aaronbot3000/velociryder/solidworks model/sprocket-encoder-12-new.sldprt

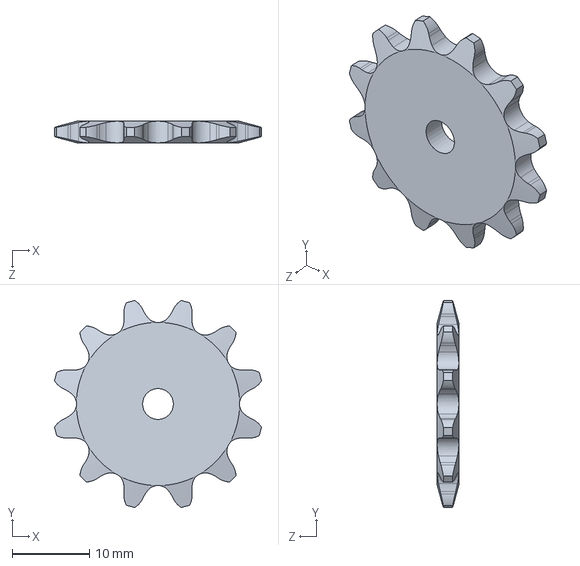
[picture p15: CAD file, 2012-03-13]
solidworks model/sprocket-encoder-12-new.sldprt
26.8 x 26.8 x 2.79 mm
