aaronbot3000/velociryder/solidworks model/sprocket-wheel-43.sldprt

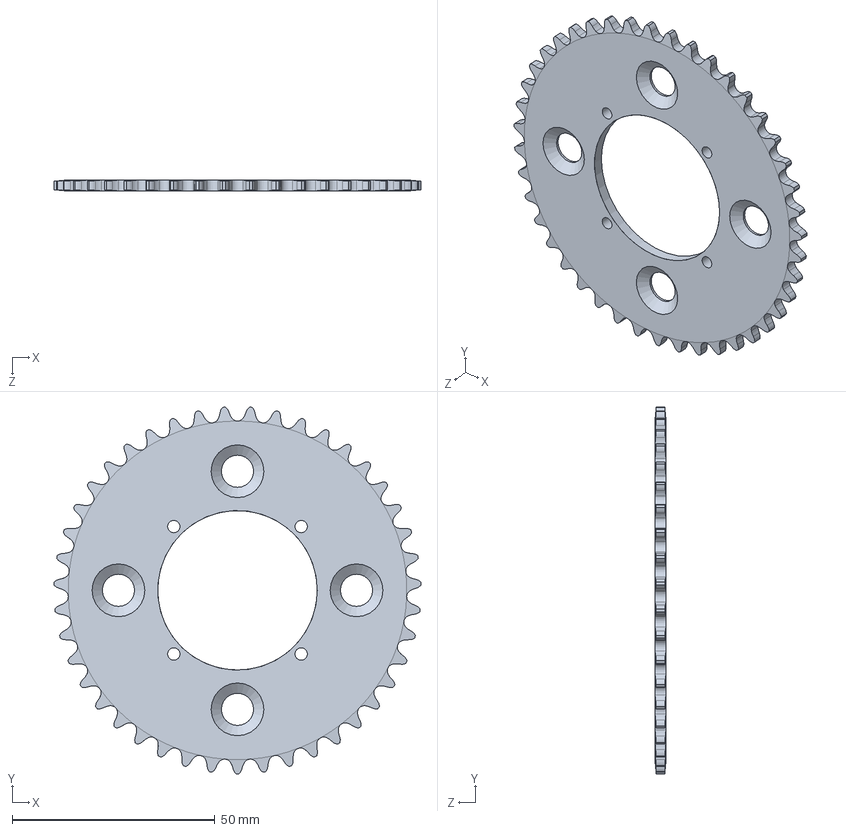
[picture p16: CAD file, 2012-03-13]
solidworks model/sprocket-wheel-43.sldprt
90.5 x 90.5 x 2.79 mm
