aaronbot3000/velociryder/solidworks model/axle.sldprt

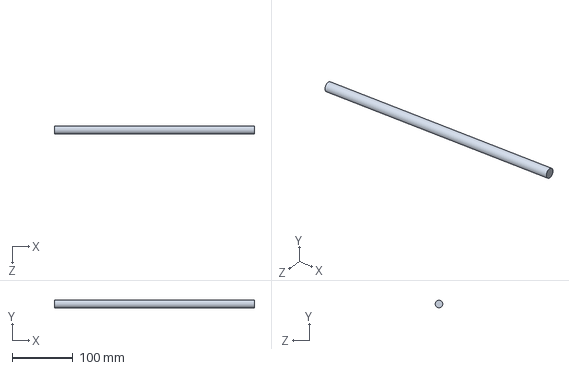
[picture p17: CAD file, 2012-03-13]
solidworks model/axle.sldprt
330.2 x 12.7 x 12.7 mm
