aaronbot3000/velociryder/solidworks model/sprocket-wheel-45.sldprt

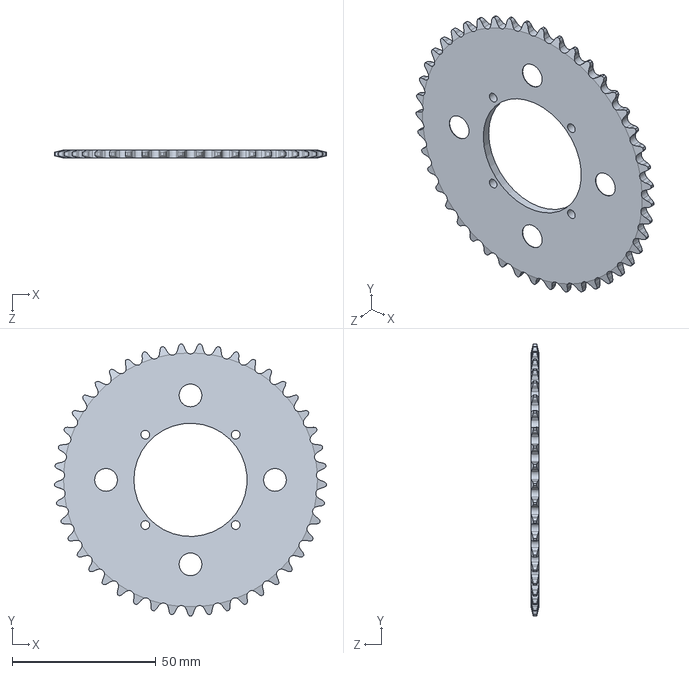
[picture p18: CAD file, 2012-03-13]
solidworks model/sprocket-wheel-45.sldprt
94.6 x 94.5 x 2.79 mm
