aaronbot3000/velociryder/solidworks model/motor-mount-p1.sldprt

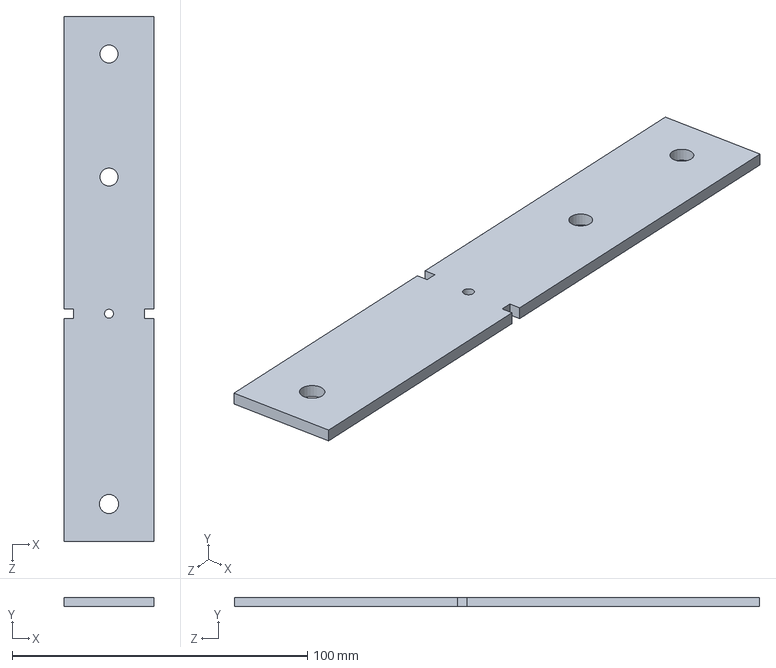
[picture p19: CAD file, 2012-03-13]
solidworks model/motor-mount-p1.sldprt
30.5 x 3.17 x 177.8 mm
