aaronbot3000/velociryder/solidworks model/sprocket-15.sldprt

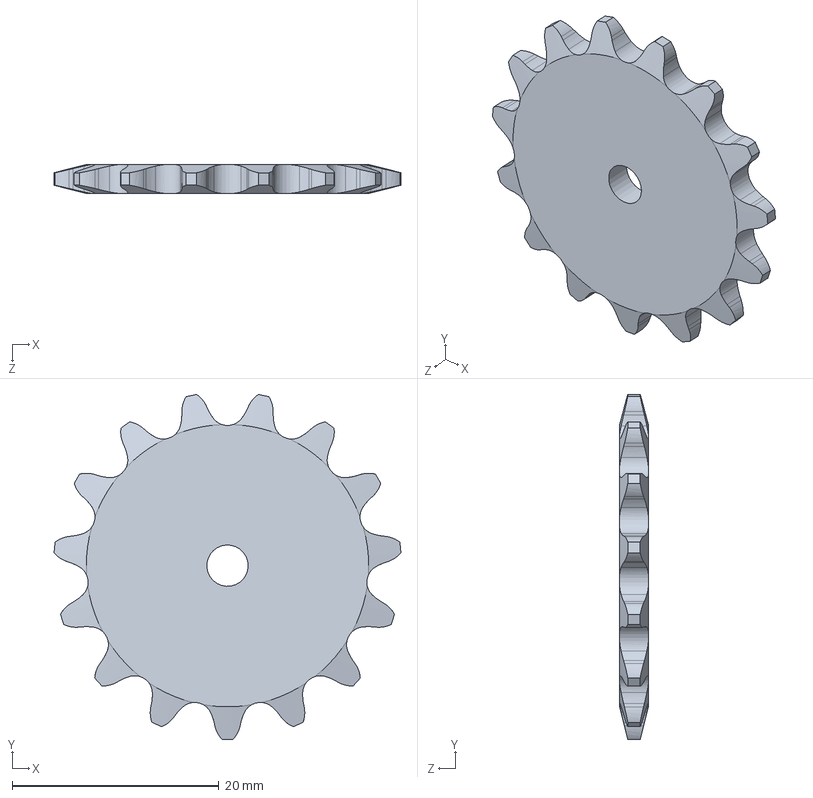
[picture p20: CAD file, 2012-03-13]
solidworks model/sprocket-15.sldprt
33.6 x 33.4 x 2.79 mm
