aaronbot3000/velociryder/solidworks model/encoder-mount.sldprt

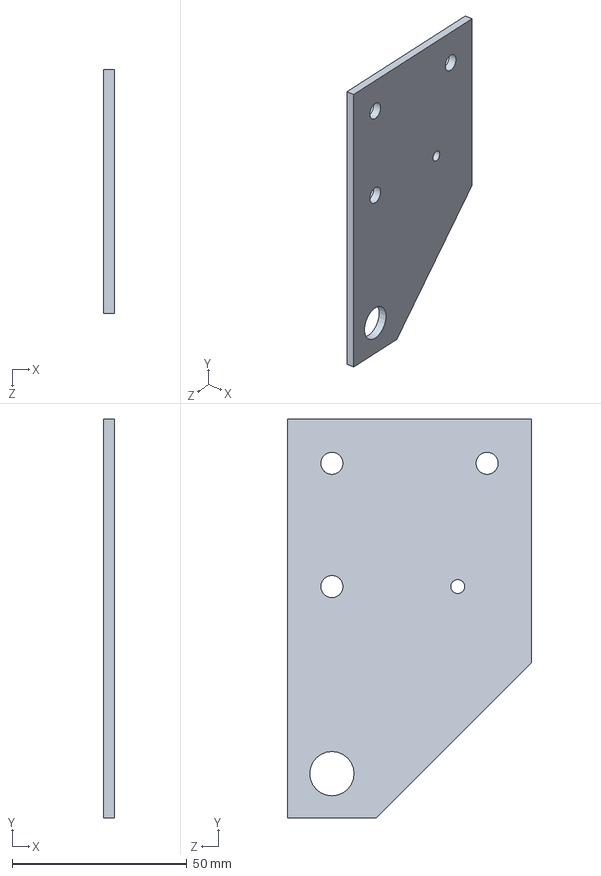
[picture p21: CAD file, 2012-03-13]
solidworks model/encoder-mount.sldprt
3.17 x 114.3 x 69.8 mm
