aaronbot3000/velociryder/solidworks model/8020-cross_support.sldprt

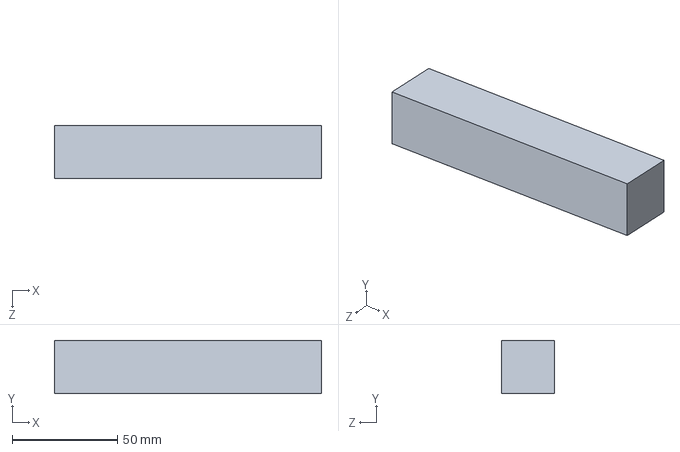
[picture p22: CAD file, 2012-03-13]
solidworks model/8020-cross_support.sldprt
127.0 x 25.4 x 25.4 mm
