aaronbot3000/velociryder/solidworks model/8020-wheel_support.sldprt

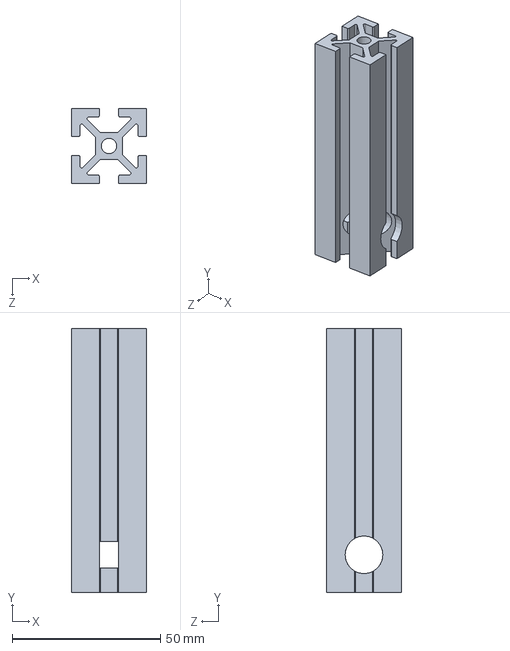
[picture p23: CAD file, 2012-03-13]
solidworks model/8020-wheel_support.sldprt
25.4 x 88.9 x 25.4 mm
