aaronbot3000/velociryder/solidworks model/encoder-support-1.sldprt

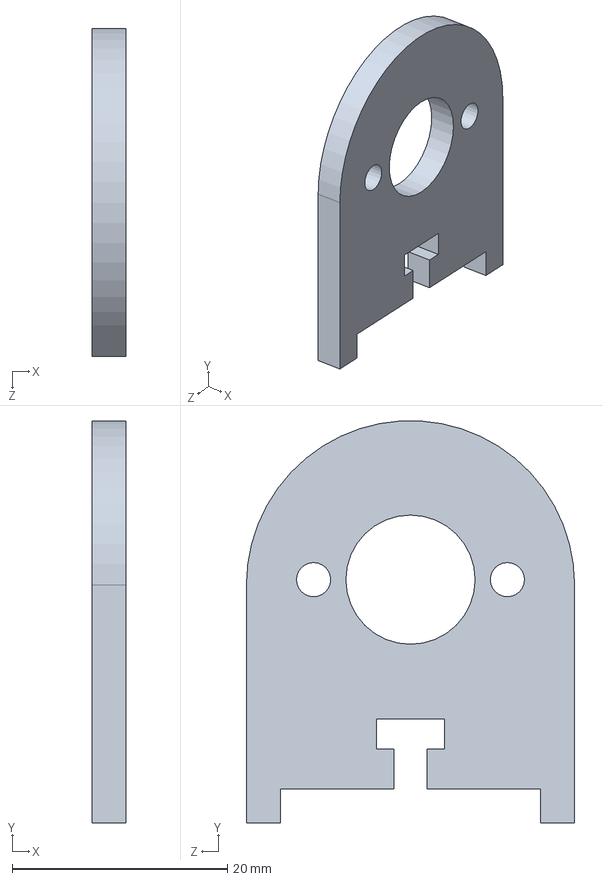
[picture p24: CAD file, 2012-03-13]
solidworks model/encoder-support-1.sldprt
3.17 x 37.3 x 30.5 mm
