aaronbot3000/velociryder/solidworks model/encoder-shaft.sldprt

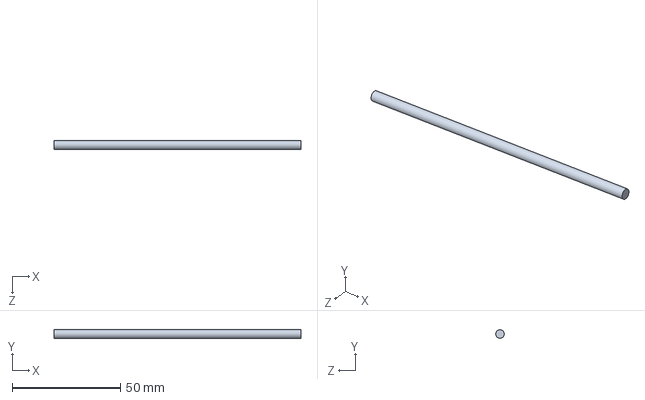
[picture p25: CAD file, 2012-03-02]
solidworks model/encoder-shaft.sldprt
114.3 x 4.00 x 4.00 mm
