aaronbot3000/velociryder/solidworks model/sprocket-wheel-40.sldprt

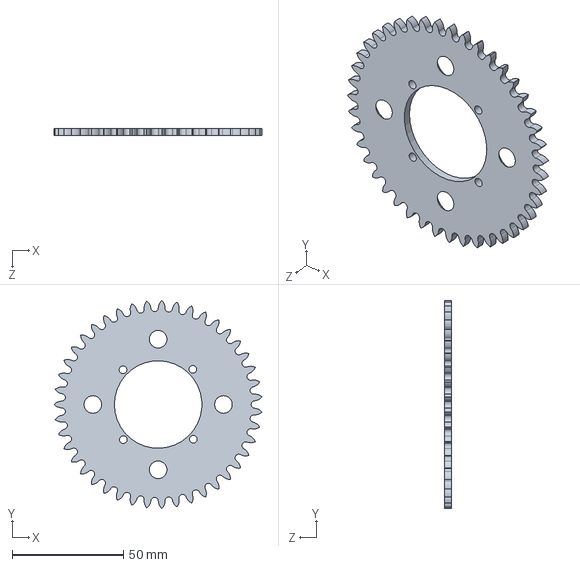
[picture p26: CAD file, 2012-03-02]
solidworks model/sprocket-wheel-40.sldprt
93.6 x 93.6 x 3.17 mm
