aaronbot3000/velociryder/solidworks model/encoder.sldprt

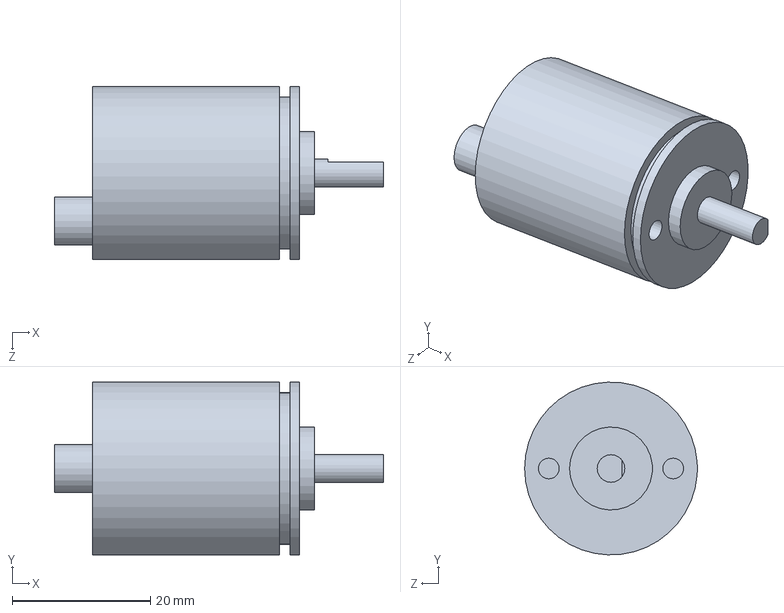
[picture p27: CAD file, 2012-02-11]
solidworks model/encoder.sldprt
47.6 x 25.0 x 25.0 mm
