aaronbot3000/velociryder/solidworks model/motor-mount.sldprt

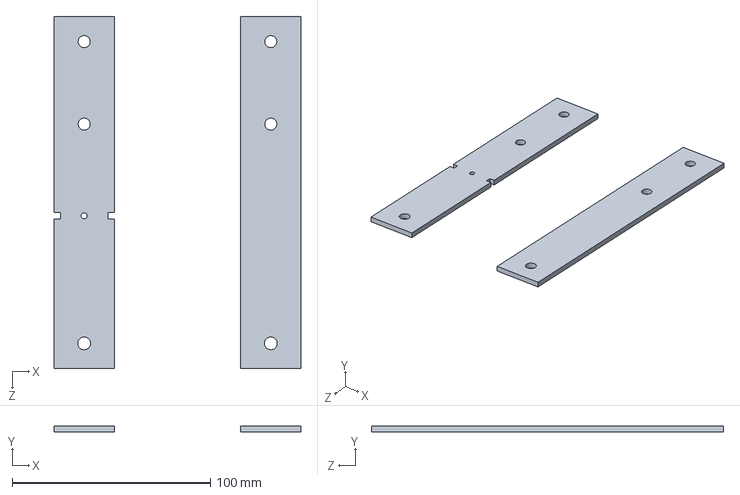
[picture p29: CAD file, 2012-02-11]
solidworks model/motor-mount.sldprt
124.7 x 3.17 x 177.8 mm
