aaronbot3000/velociryder/solidworks model/wheel.sldprt

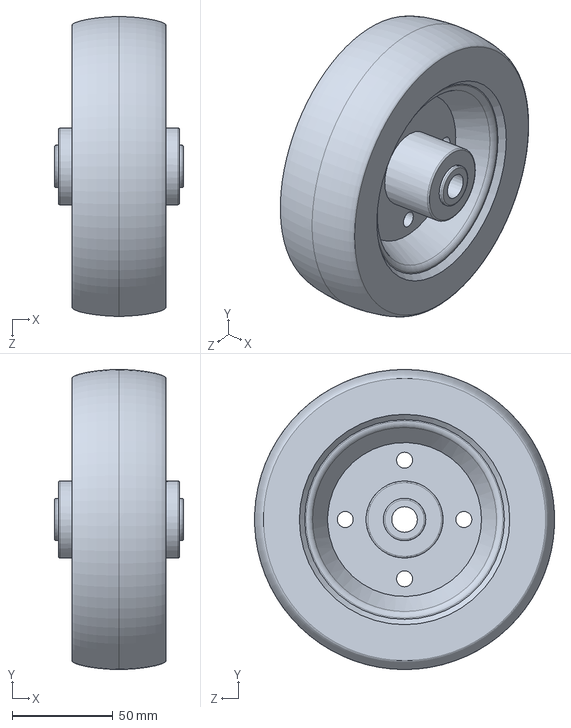
[picture p30: CAD file, 2012-02-11]
solidworks model/wheel.sldprt
63.9 x 148.6 x 148.5 mm
