aaronbot3000/velociryder/solidworks model/gear-motor-18.sldprt

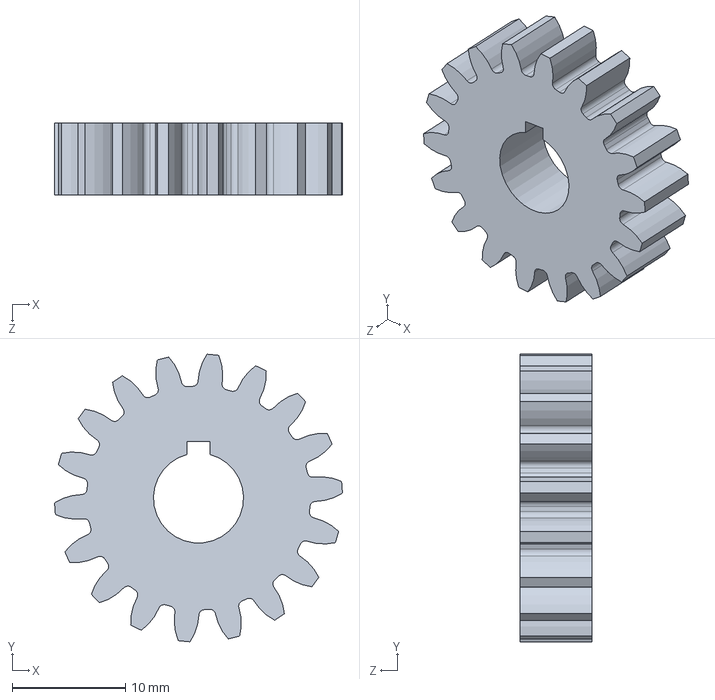
[picture p31: CAD file, 2012-02-11]
solidworks model/gear-motor-18.sldprt
25.4 x 25.4 x 6.35 mm
