aaronbot3000/velociryder/solidworks model/sprocket-motor-12.sldprt

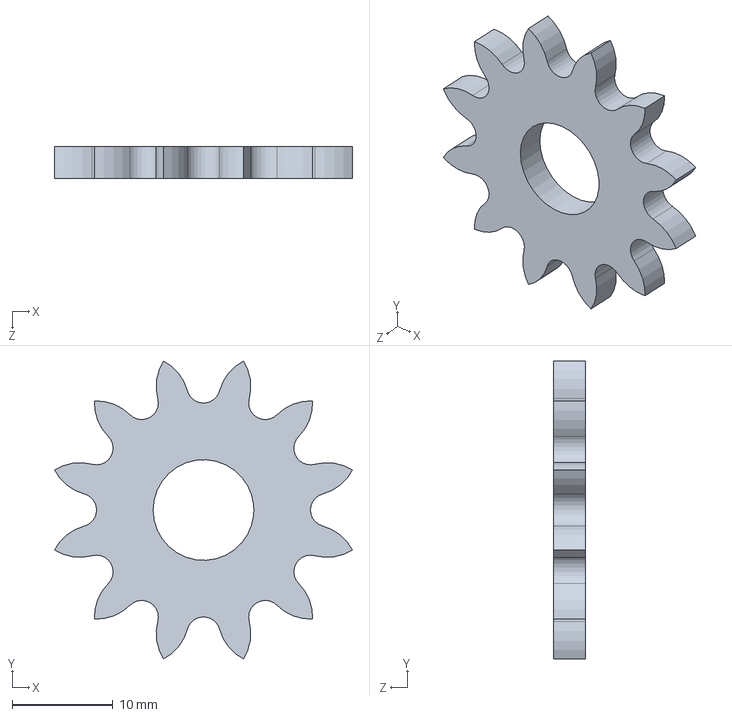
[picture p32: CAD file, 2012-02-11]
solidworks model/sprocket-motor-12.sldprt
29.6 x 29.6 x 3.17 mm
