aaronbot3000/velociryder/solidworks model/gear-wheel-64.sldprt

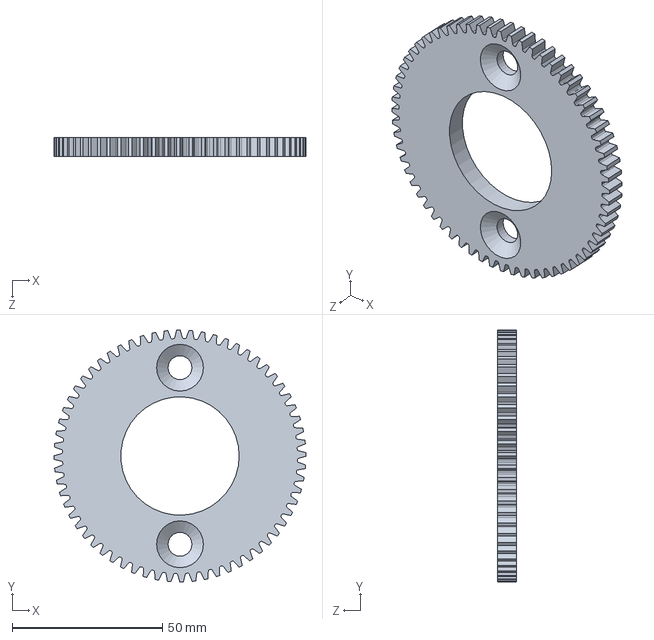
[picture p33: CAD file, 2012-02-11]
solidworks model/gear-wheel-64.sldprt
83.8 x 83.8 x 6.35 mm
