aaronbot3000/velociryder/solidworks model/wheel-standoff.sldprt

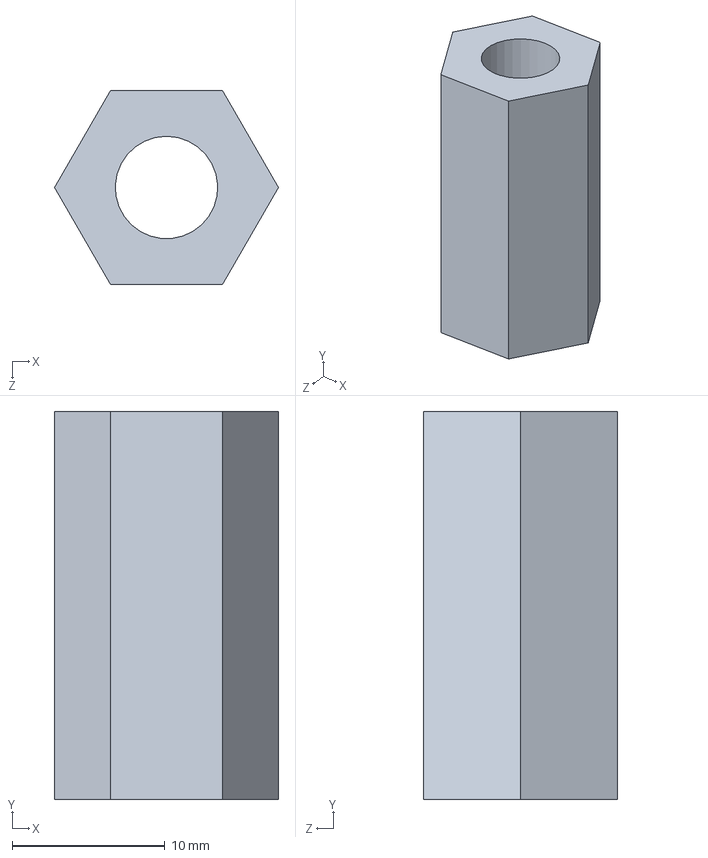
[picture p34: CAD file, 2012-02-11]
solidworks model/wheel-standoff.sldprt
14.7 x 25.4 x 12.7 mm
