aaronbot3000/velociryder/solidworks model/sprocket-12.dxf

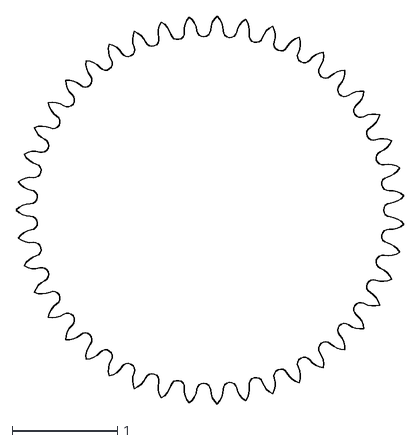
[picture p35: CAD file, 2012-02-11]
solidworks model/sprocket-12.dxf
3.68 x 3.69
