aaronbot3000/velociryder/solidworks model/strain-gauge.sldprt

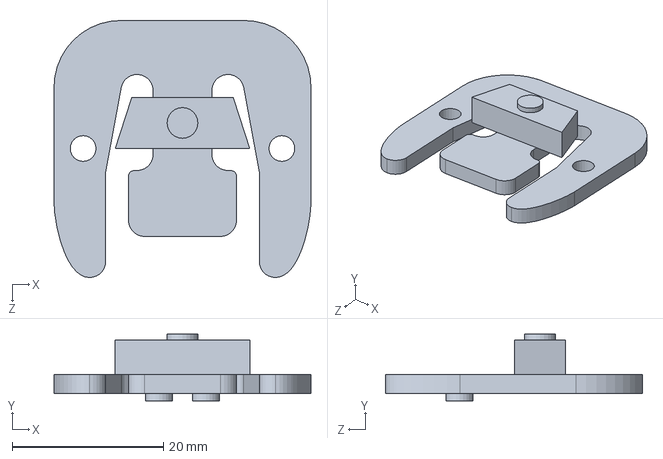
[picture p36: CAD file, 2012-02-11]
solidworks model/strain-gauge.sldprt
34.0 x 8.85 x 34.0 mm
