aaronbot3000/velociryder/solidworks model/shaft-coupler.sldprt

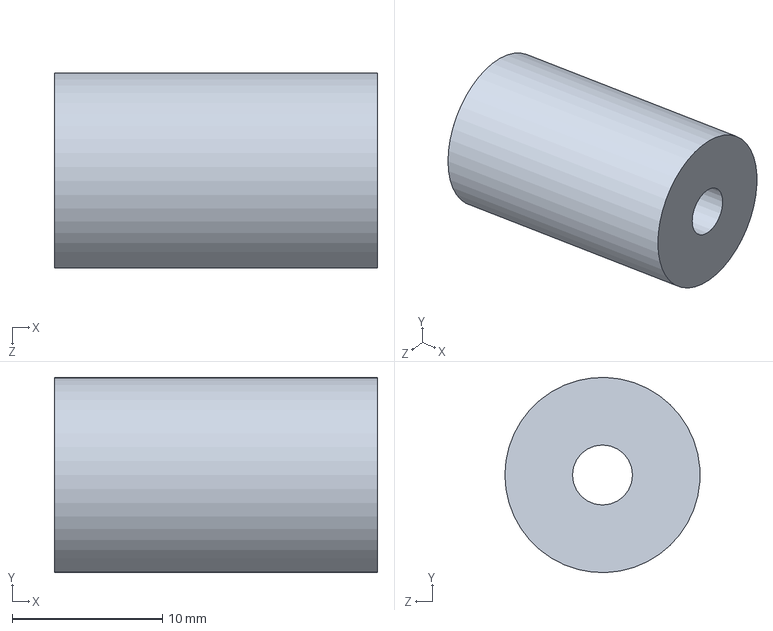
[picture p37: CAD file, 2012-02-11]
solidworks model/shaft-coupler.sldprt
21.5 x 13.0 x 13.0 mm
