aaronbot3000/velociryder/solidworks model/scooter-motor.sldprt

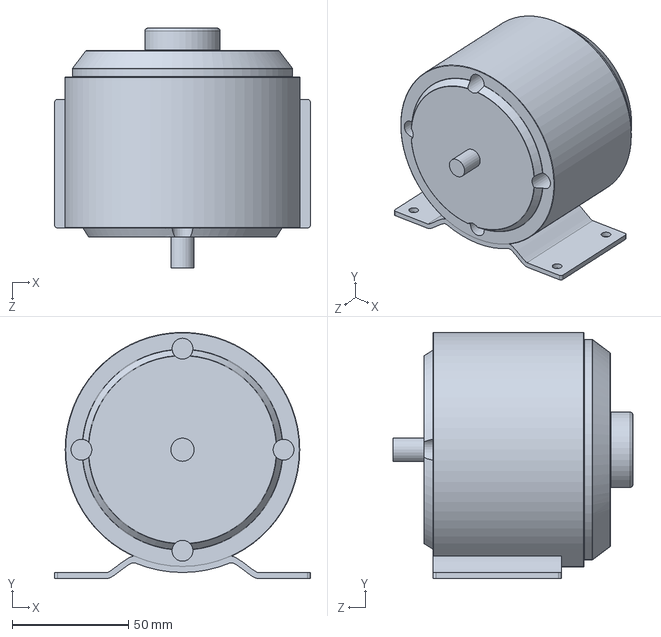
[picture p38: CAD file, 2012-02-11]
solidworks model/scooter-motor.sldprt
110.2 x 106.0 x 103.2 mm
