aaronbot3000/velociryder/solidworks model/CIM-motor.sldprt

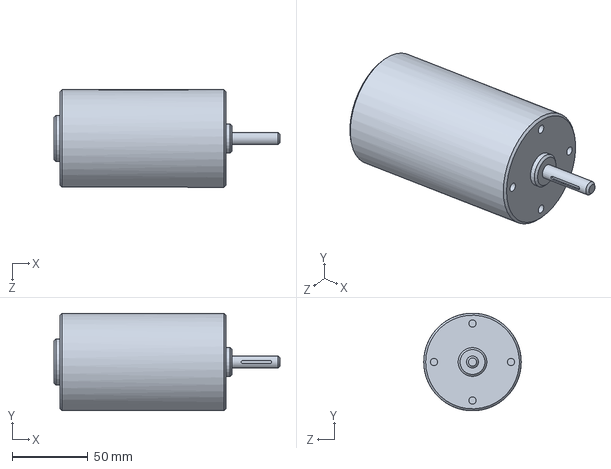
[picture p39: CAD file, 2012-01-24]
solidworks model/CIM-motor.sldprt
149.2 x 64.4 x 64.4 mm
