aaronbot3000/velociryder/solidworks model/gear-motor-15.sldprt

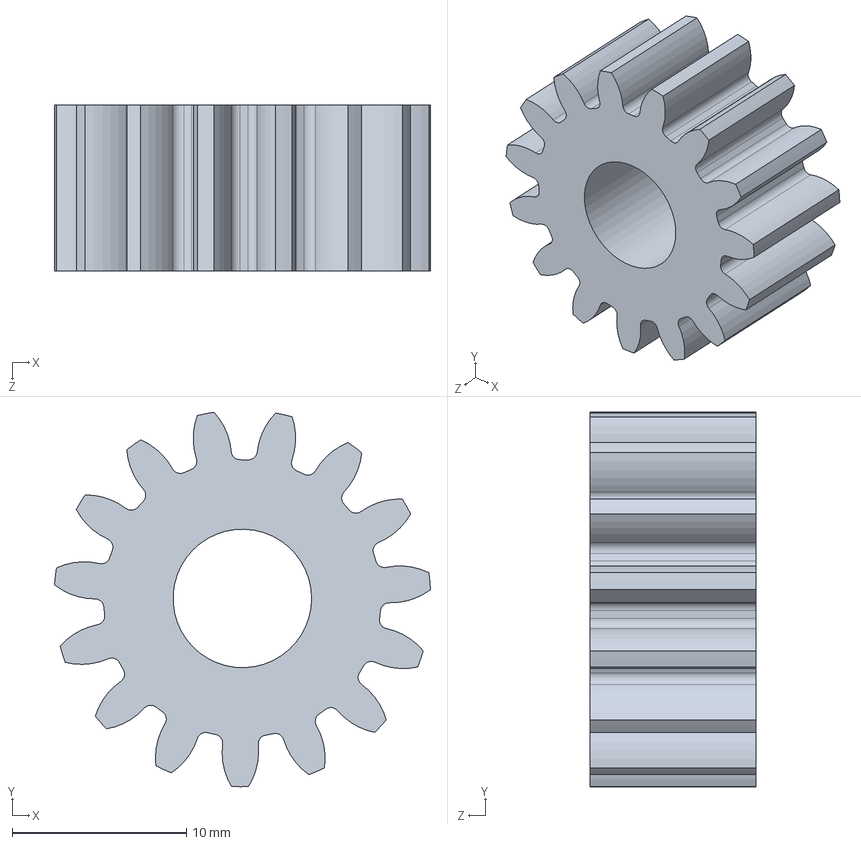
[picture p40: CAD file, 2012-01-24]
solidworks model/gear-motor-15.sldprt
21.5 x 21.5 x 9.53 mm
