aaronbot3000/velociryder/solidworks model/gear-wheel-56.sldprt

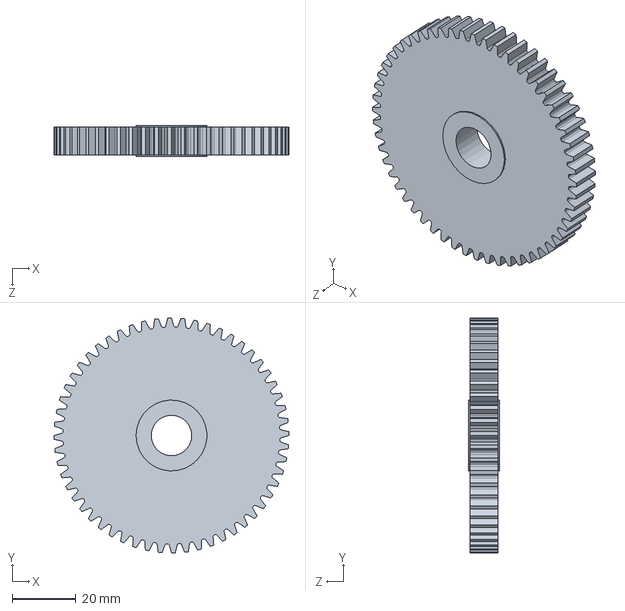
[picture p41: CAD file, 2012-01-24]
solidworks model/gear-wheel-56.sldprt
73.7 x 73.7 x 9.65 mm
