aaronbot3000/velociryder/solidworks model/deck.sldprt

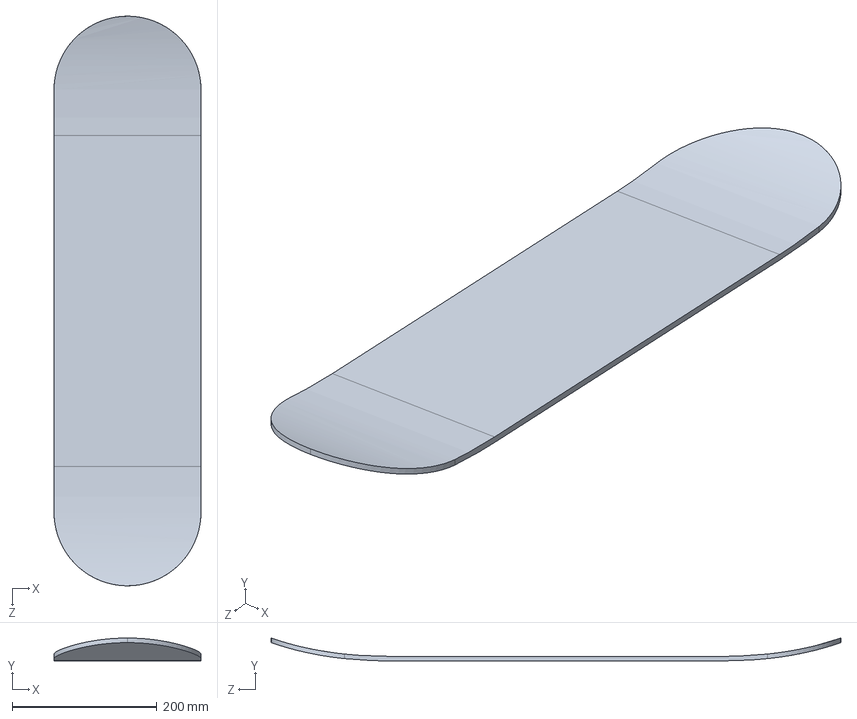
[picture p42: CAD file, 2012-01-23]
solidworks model/deck.sldprt
203.2 x 31.8 x 787.4 mm
