aaronbot3000/velociryder/solidworks model/battery.sldprt

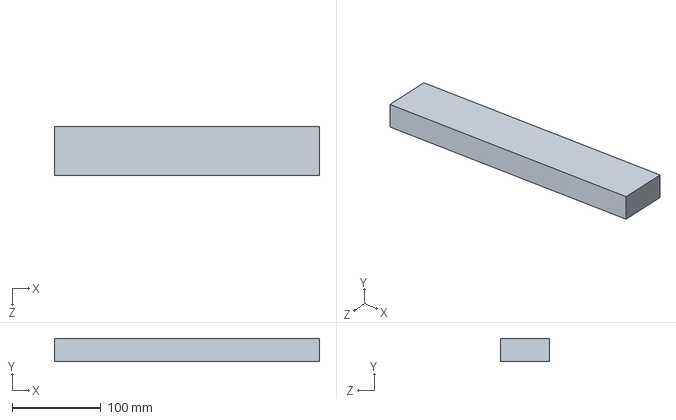
[picture p43: CAD file, 2012-01-23]
solidworks model/battery.sldprt
299.0 x 26.0 x 55.0 mm
